stuartatpeasy/speaker_prototype_2way_sealed/cabinet/baffle.pdf

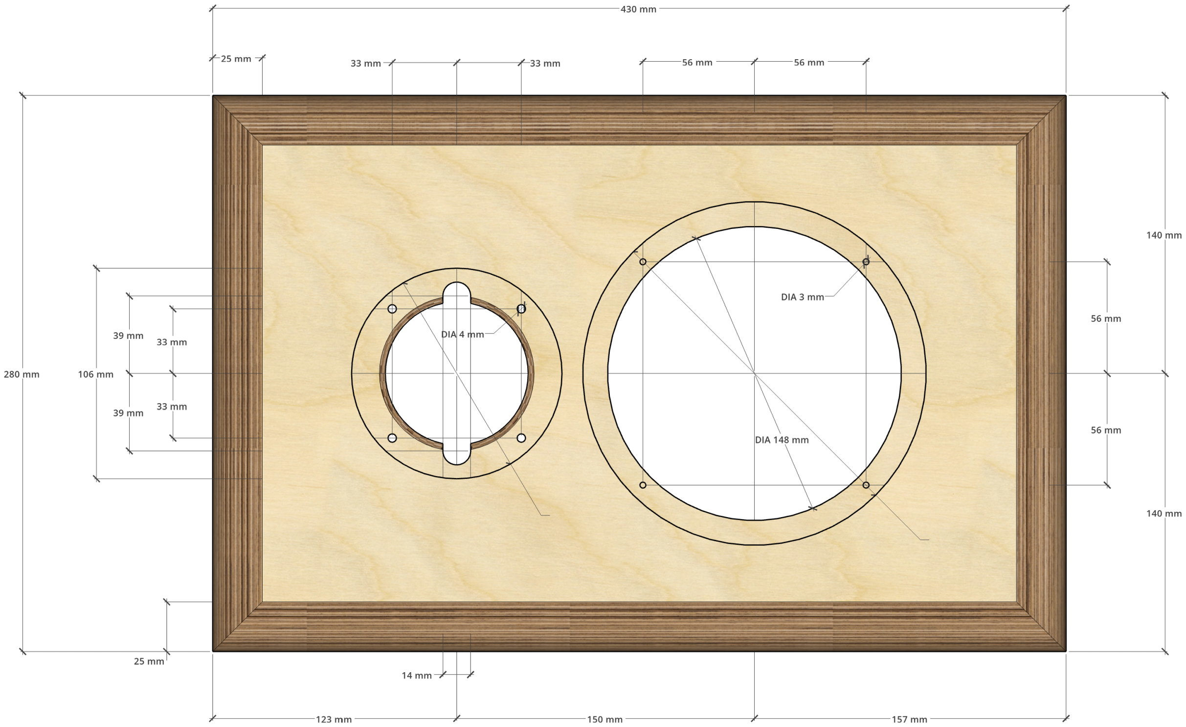
[picture p2: page 1]
