stuartatpeasy/speaker_prototype_2way_sealed/cabinet/brace_centre.pdf

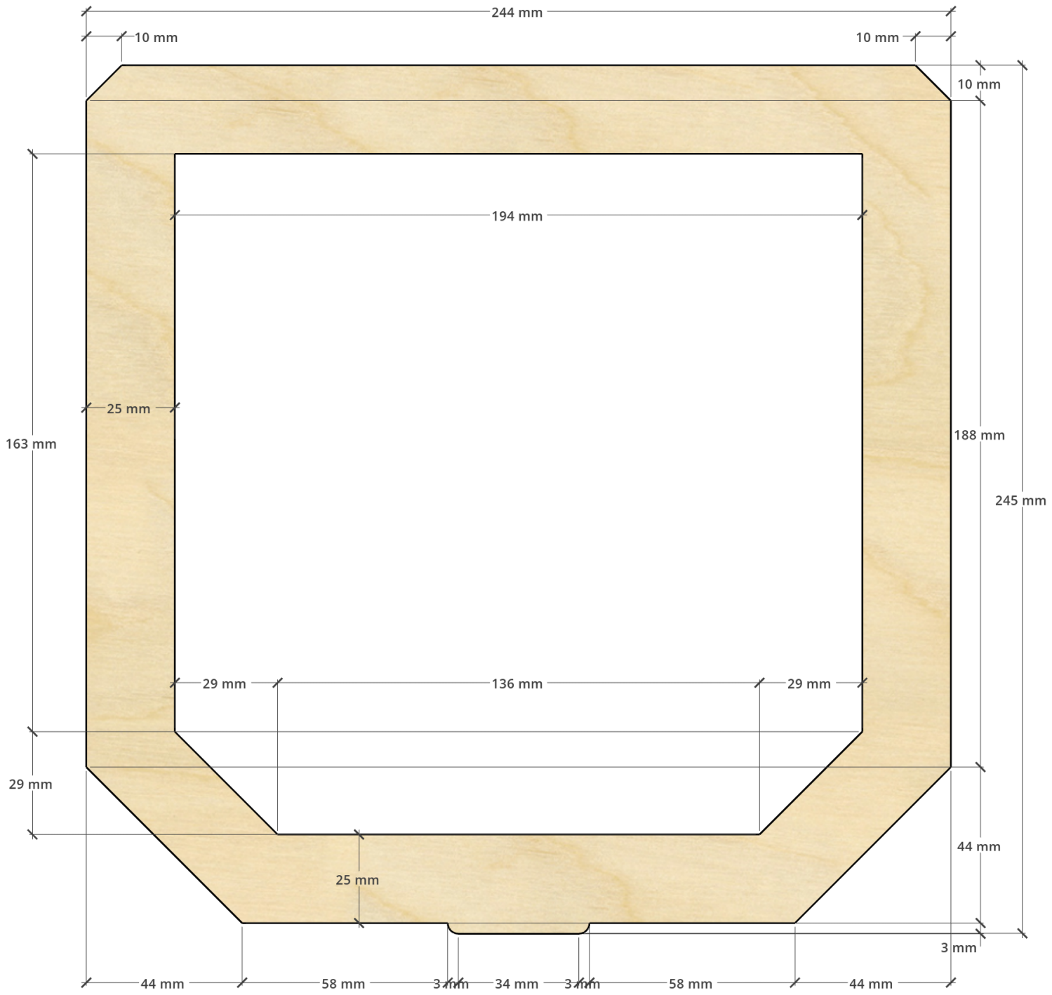
[picture p3: page 1]
