stuartatpeasy/speaker_prototype_2way_sealed/cabinet/brace_lower.pdf

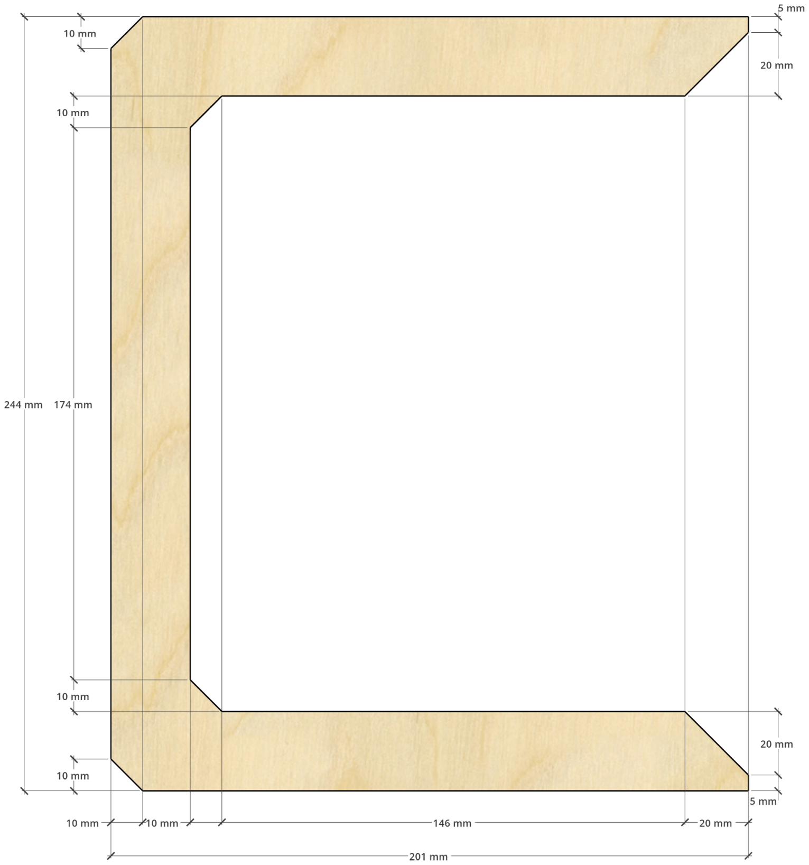
[picture p4: page 1]
