stuartatpeasy/speaker_prototype_2way_sealed/cabinet/brace_rear.pdf

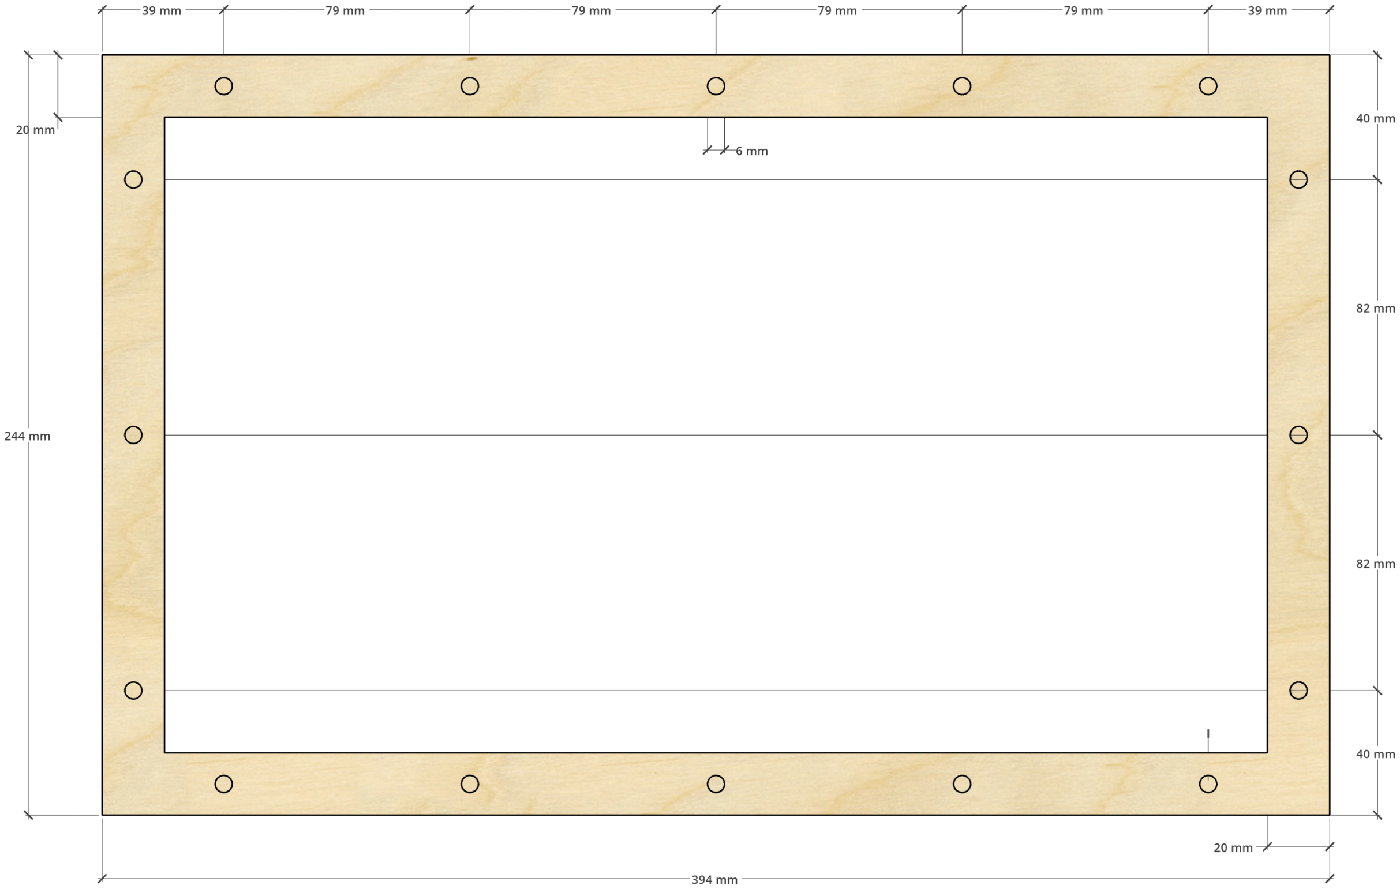
[picture p5: page 1]
