stuartatpeasy/speaker_prototype_2way_sealed/cabinet/brace_rear_upper_lower.pdf

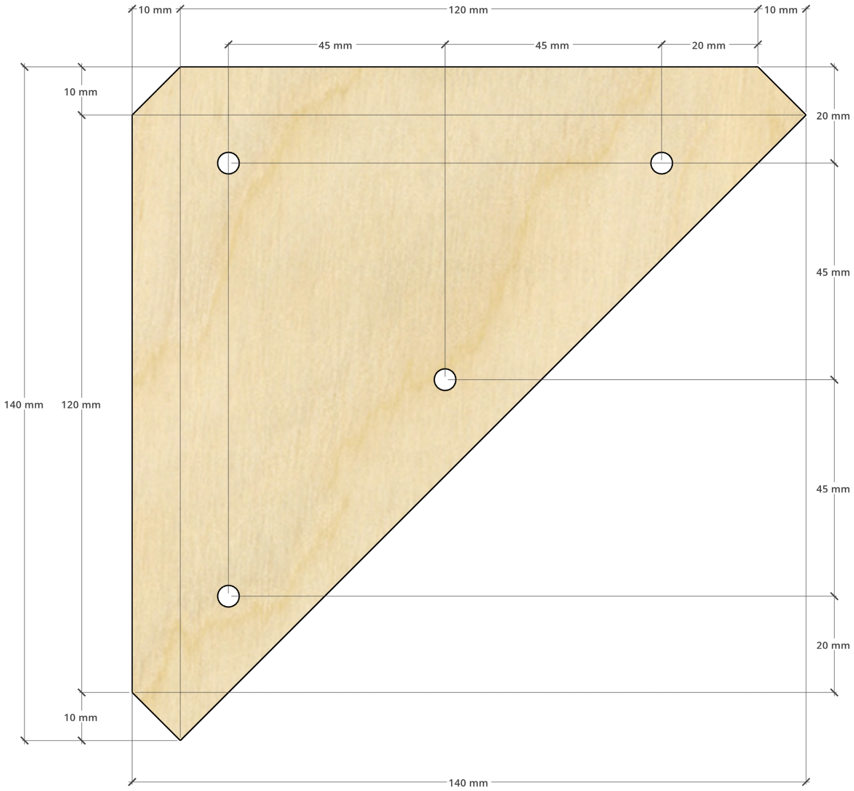
[picture p6: page 1]
