stuartatpeasy/speaker_prototype_2way_sealed/cabinet/brace_upper.pdf

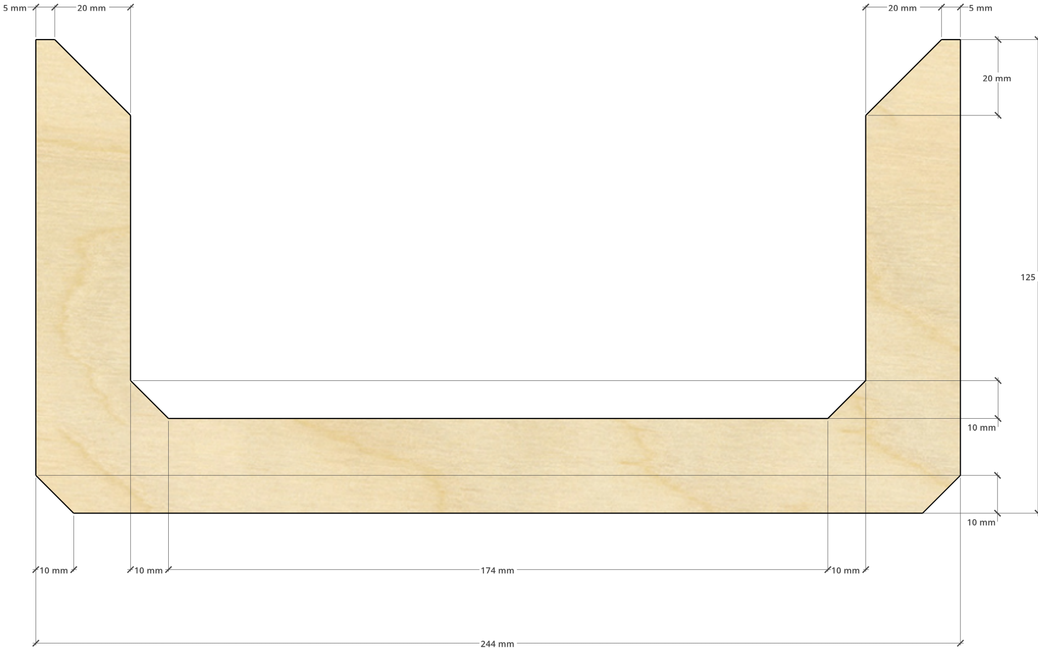
[picture p7: page 1]
