stuartatpeasy/speaker_prototype_2way_sealed/cabinet/panel_left_right.pdf

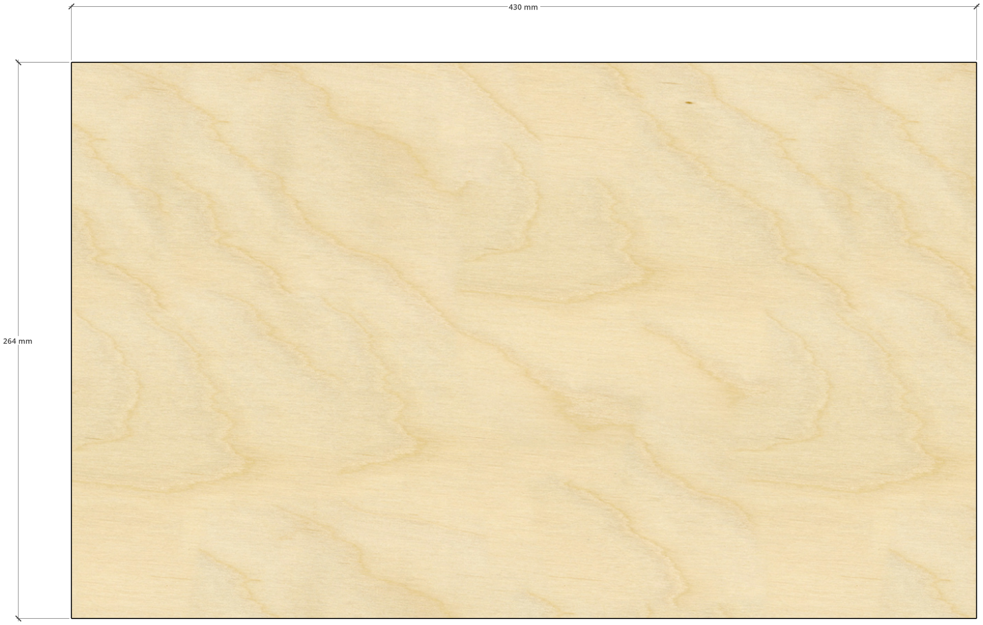
[picture p8: page 1]
