stuartatpeasy/speaker_prototype_2way_sealed/cabinet/panel_rear.pdf

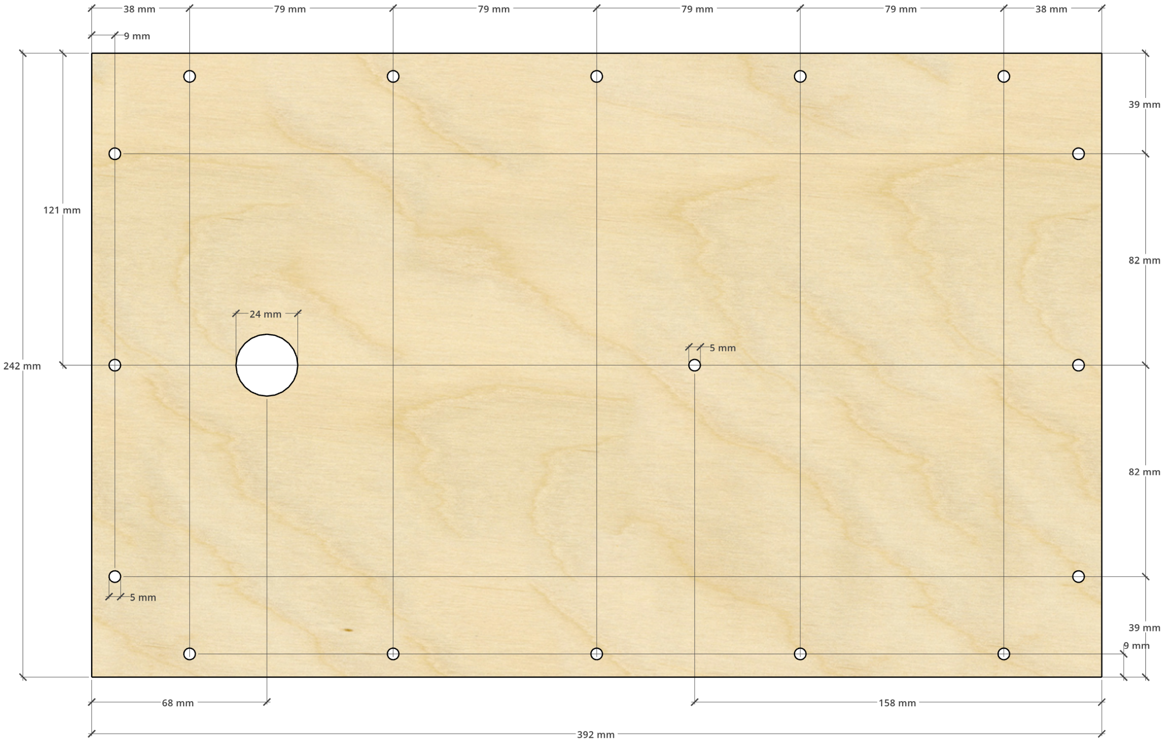
[picture p9: page 1]
