stuartatpeasy/speaker_prototype_2way_sealed/cabinet/panel_top_bottom.pdf

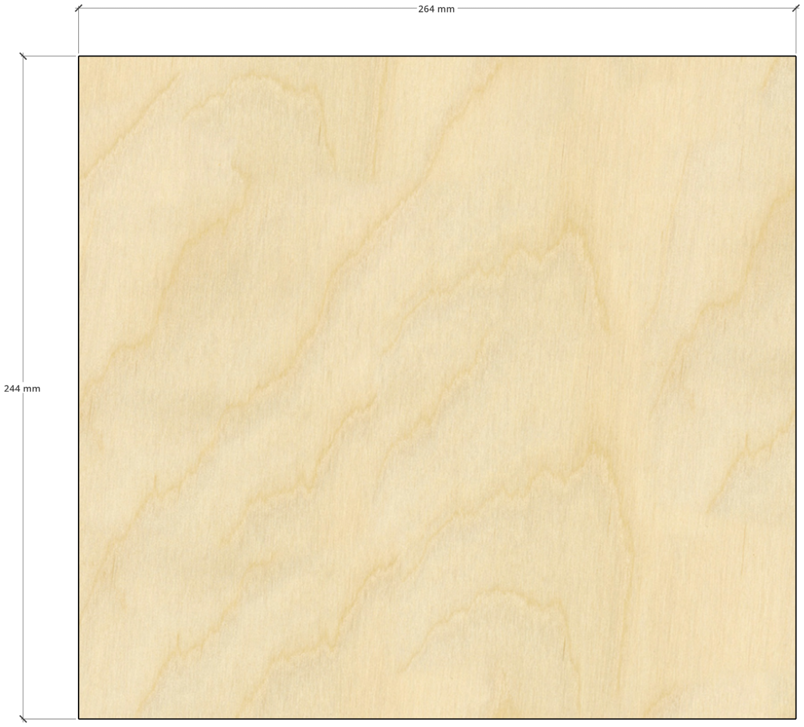
[picture p10: page 1]
