stuartatpeasy/speaker_prototype_2way_sealed/calibration/ECM8000_calibration_data.csv

Hz | dB | Phase
20.0000 | -0.070 | 31.90
25.1785 | 0.137 | 25.80
31.6978 | 0.275 | 20.20
39.9052 | 0.393 | 16.20
50.2377 | 0.344 | 12.30
63.2455 | 0.534 | 9.23
79.6214 | 0.512 | 6.47
100.2370 | 0.493 | 4.27
126.1910 | 0.358 | 3.03
158.8650 | 0.407 | 0.06
200.0000 | 0.114 | -1.70
251.7850 | 0.295 | -3.10
300.6400 | 0.204 | -3.10
312.4950 | 0.170 | -3.40
324.8170 | 0.136 | -5.00
337.6250 | 0.103 | -4.20
350.9380 | 0.073 | -2.40
364.7770 | 0.047 | -3.60
379.1600 | 0.021 | -4.20
394.1110 | 0.000 | -2.30
409.6520 | -0.010 | -2.80
425.8050 | -0.010 | -3.50
442.5950 | -0.010 | -1.70
460.0480 | -0.020 | -2.70
478.1880 | -0.020 | -2.50
497.0440 | -0.020 | -1.60
516.6430 | -0.020 | -3.00
537.0160 | -0.020 | -1.30
558.1910 | -0.030 | -2.60
580.2020 | -0.040 | -1.50
603.0800 | -0.050 | -2.20
626.8610 | -0.060 | -1.40
651.5790 | -0.060 | -2.10
677.2720 | -0.070 | -1.00
703.9780 | -0.070 | -2.10
731.7370 | -0.080 | -1.00
760.5910 | -0.090 | -1.40
790.5820 | -0.110 | -1.50
821.7560 | -0.120 | -0.50
854.1600 | -0.120 | -0.80
887.8410 | -0.110 | -0.90
922.8500 | -0.080 | -0.10
959.2400 | -0.040 | 0.22
997.0640 | 0.000 | -0.10
1036.3800 | 0.019 | -0.50
1077.2400 | 0.034 | -0.80
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
